mensikv/ESP8266_Neopixel_Controller/img/ADSM201_WS2812B_ring_1.JPG

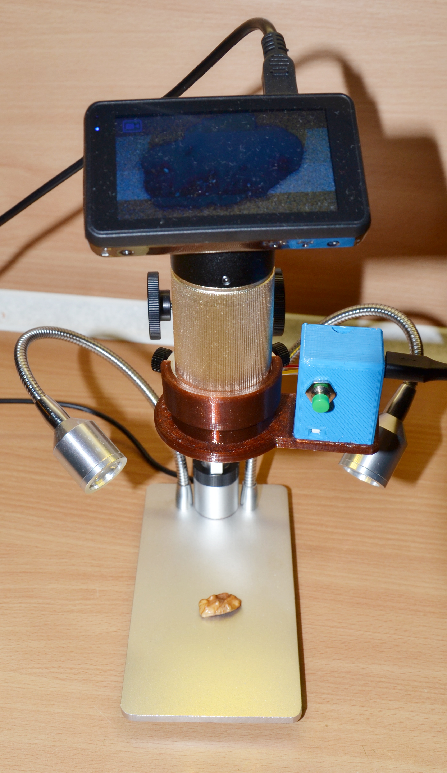
img/ADSM201_WS2812B_ring_1.JPG
