mensikv/ESP8266_Neopixel_Controller/img/Web - choose color.png

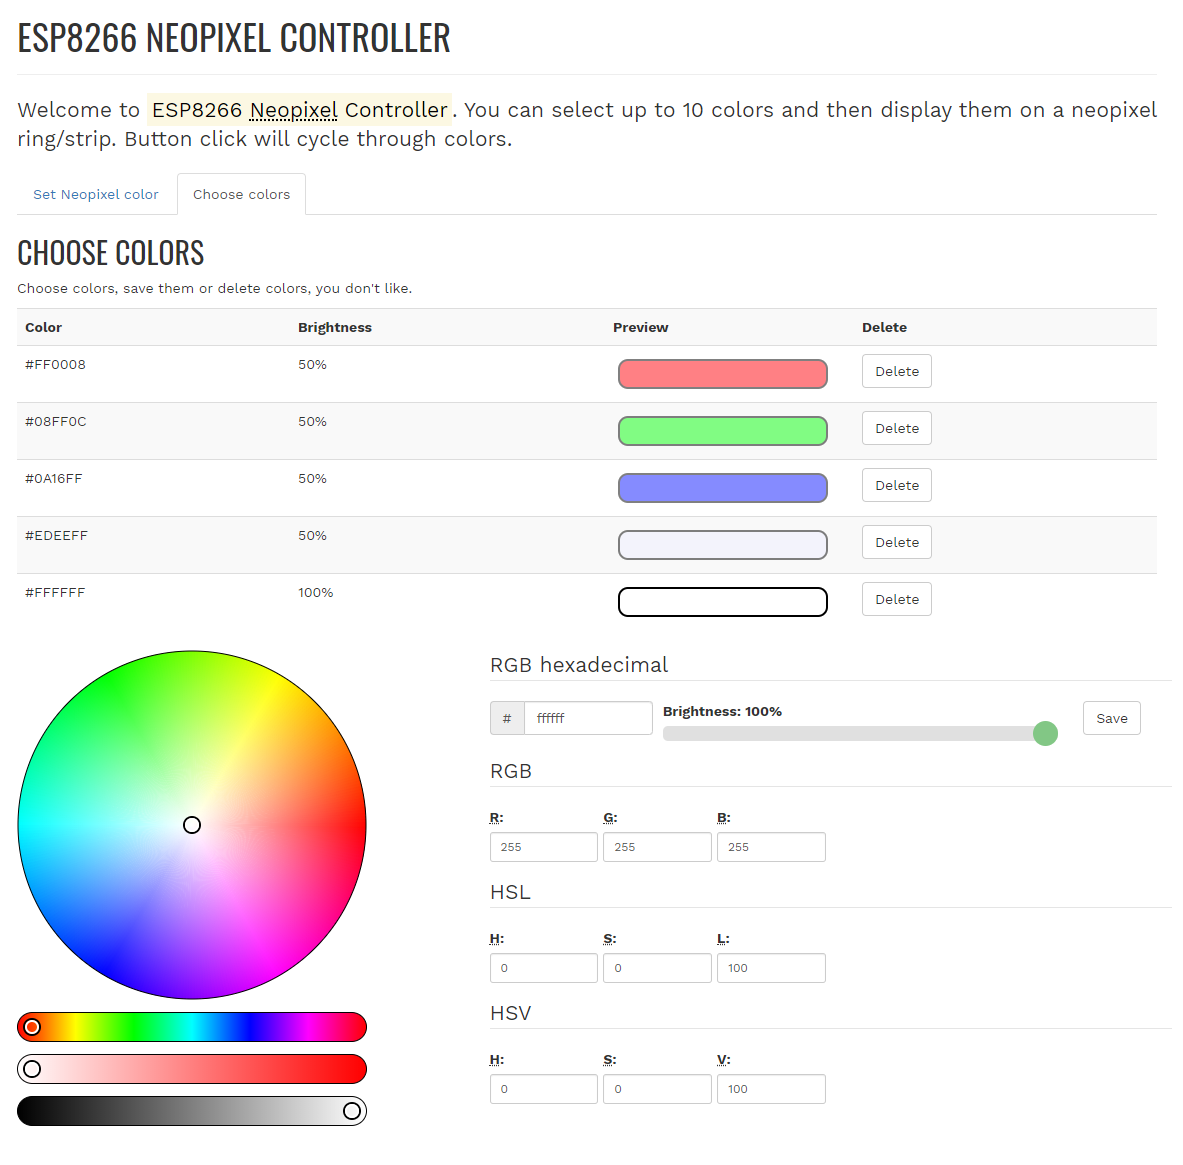
img/Web - choose color.png
