mensikv/ESP8266_Neopixel_Controller/img/Web - set color.png

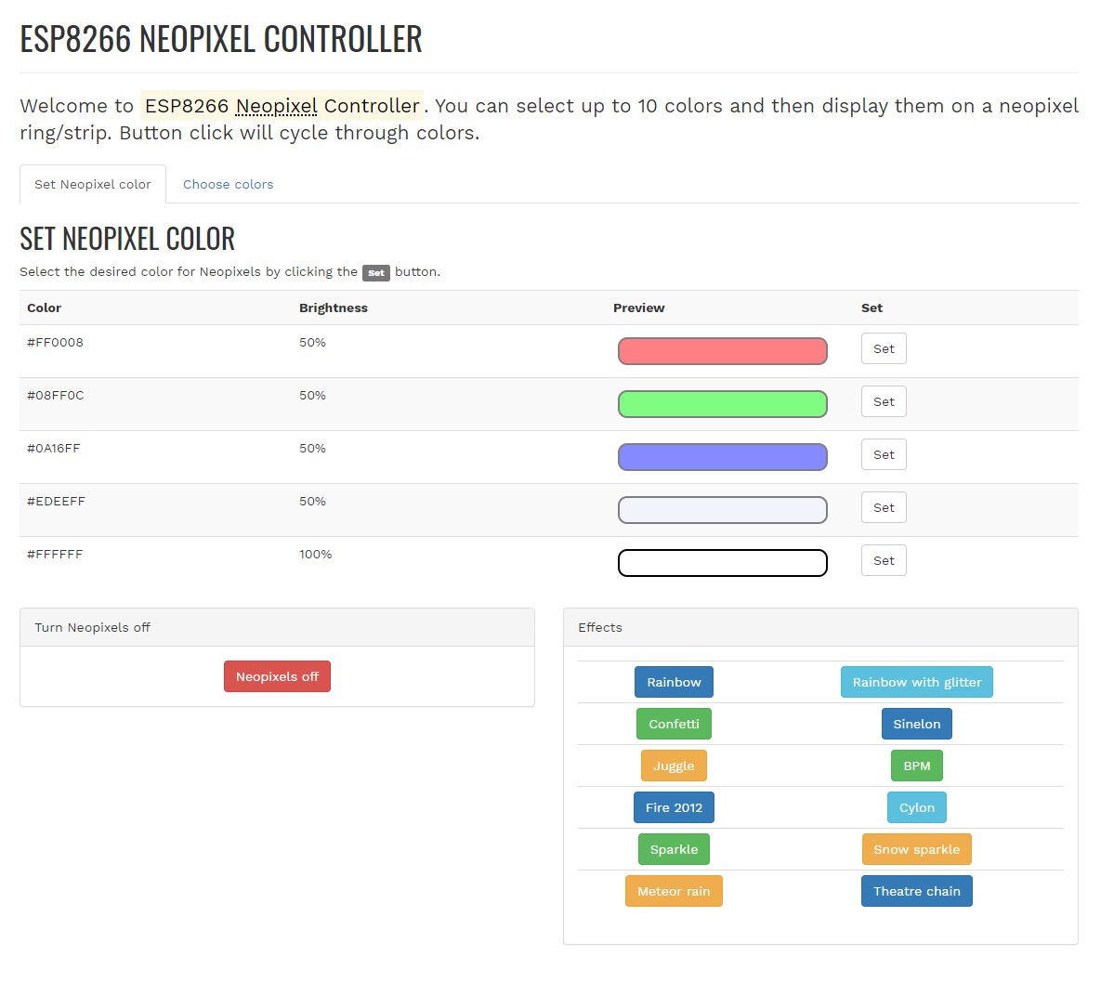
img/Web - set color.png
