mensikv/ESP8266_Neopixel_Controller/img/WS2812B_controller_4.JPG

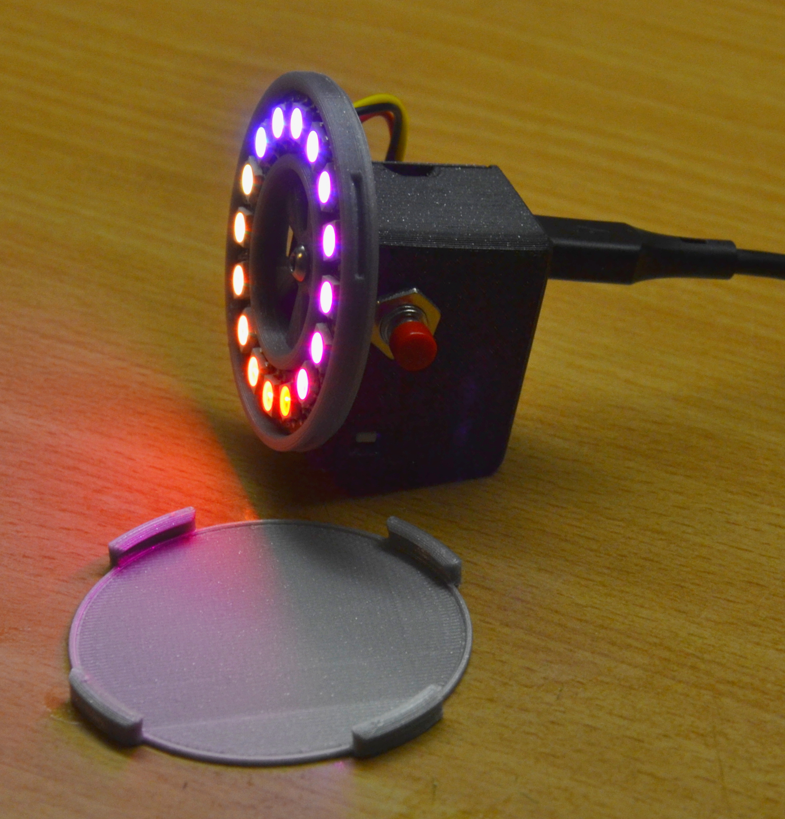
img/WS2812B_controller_4.JPG
