mensikv/ESP8266_Neopixel_Controller/img/WS2812B_controller_8.png

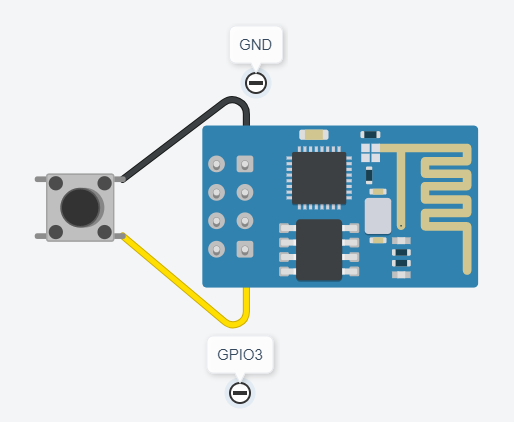
img/WS2812B_controller_8.png
